jaebrn/cart-360-final/Final Artifact/IMAGES_VIDEO/Photos and video of board/IMG_3775.jpg

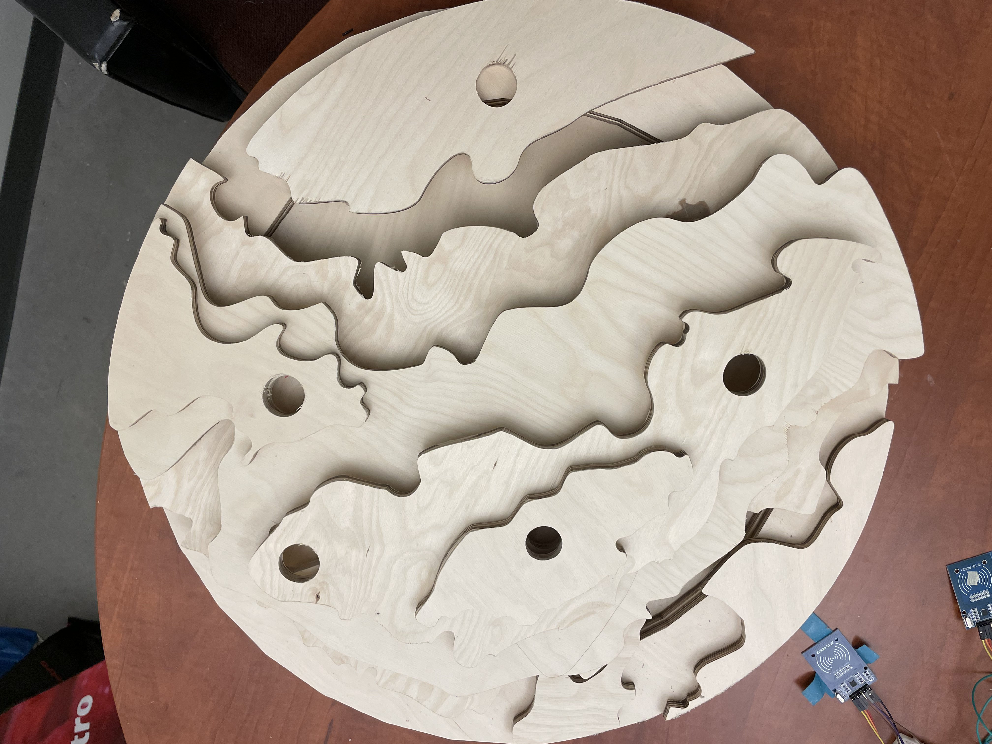
Final Artifact/IMAGES_VIDEO/Photos and video of board/IMG_3775.jpg
